meerstern/PS2USB_CONVERTER/firm_v2/src/config/default/initialization.c

/*******************************************************************************
  System Initialization File

  File Name:
    initialization.c

  Summary:
    This file contains source code necessary to initialize the system.

  Description:
    This file contains source code necessary to initialize the system.  It
    implements the "SYS_Initialize" function, defines the configuration bits,
    and allocates any necessary global system resources,
 *******************************************************************************/

// DOM-IGNORE-BEGIN
/*******************************************************************************
* Copyright (C) 2018 Microchip Technology Inc. and its subsidiaries.
*
* Subject to your compliance with these terms, you may use Microchip software
* and any derivatives exclusively with Microchip products. It is your
* responsibility to comply with third party license terms applicable to your
* use of third party software (including open source software) that may
* accompany Microchip software.
*
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
* IN NO EVENT WILL MICROCHIP BE LIABLE FOR ANY INDIRECT, SPECIAL, PUNITIVE,
* INCIDENTAL OR CONSEQUENTIAL LOSS, DAMAGE, COST OR EXPENSE OF ANY KIND
* WHATSOEVER RELATED TO THE SOFTWARE, HOWEVER CAUSED, EVEN IF MICROCHIP HAS
* BEEN ADVISED OF THE POSSIBILITY OR THE DAMAGES ARE FORESEEABLE. TO THE
* FULLEST EXTENT ALLOWED BY LAW, MICROCHIP'S TOTAL LIABILITY ON ALL CLAIMS IN
* ANY WAY RELATED TO THIS SOFTWARE WILL NOT EXCEED THE AMOUNT OF FEES, IF ANY,
* THAT YOU HAVE PAID DIRECTLY TO MICROCHIP FOR THIS SOFTWARE.
 *******************************************************************************/
// DOM-IGNORE-END

// *****************************************************************************
// *****************************************************************************
// Section: Included Files
// *****************************************************************************
// *****************************************************************************
#include "configuration.h"
#include "definitions.h"
#include "device.h"



// ****************************************************************************
// ****************************************************************************
// Section: Configuration Bits
// ****************************************************************************
// ****************************************************************************

/*** DEVCFG0 ***/
#pragma config DEBUG =      OFF
#pragma config JTAGEN =     OFF
#pragma config ICESEL =     ICS_PGx1
#pragma config PWP =        OFF
#pragma config BWP =        OFF
#pragma config CP =         OFF


/*** DEVCFG1 ***/
#pragma config FNOSC =      FRCPLL
#pragma config FPBDIV =     DIV_1
#pragma config FSOSCEN =    OFF
#pragma config IESO =       OFF
#pragma config POSCMOD =    HS
#pragma config OSCIOFNC =   OFF
#pragma config FCKSM =      CSDCMD
#pragma config WDTPS =      PS1048576
#pragma config FWDTEN =     OFF
#pragma config WINDIS =     OFF
#pragma config FWDTWINSZ =  WINSZ_50


/*** DEVCFG2 ***/
#pragma config FPLLIDIV =   DIV_2
#pragma config FPLLMUL =    MUL_20
#pragma config FPLLODIV =   DIV_2
#pragma config UPLLEN =     ON
#pragma config UPLLIDIV =   DIV_3

/*** DEVCFG3 ***/
#pragma config FVBUSONIO =  ON
#pragma config USERID =     0xffff
#pragma config PMDL1WAY =   ON
#pragma config IOL1WAY =    ON
#pragma config FUSBIDIO =   OFF




// *****************************************************************************
// *****************************************************************************
// Section: Driver Initialization Data
// *****************************************************************************
// *****************************************************************************


// *****************************************************************************
// *****************************************************************************
// Section: System Data
// *****************************************************************************
// *****************************************************************************
/* Structure to hold the object handles for the modules in the system. */
SYSTEM_OBJECTS sysObj;

// *****************************************************************************
// *****************************************************************************
// Section: Library/Stack Initialization Data
// *****************************************************************************
// *****************************************************************************
/******************************************************
 * USB Driver Initialization
 ******************************************************/
 
uint8_t __attribute__((aligned(512))) endPointTable1[DRV_USBFS_ENDPOINTS_NUMBER * 32];

void DRV_USB_VBUSPowerEnable(uint8_t port, bool enable)
{
	/* Note: USB Host applications should have a way for Enabling/Disabling the 
	   VBUS. Applications can use a GPIO to turn VBUS on/off through a switch. 
	   In MHC Pin Settings select the pin used as VBUS Power Enable as output and 
	   name it to "VBUS_AH". If you a see a build error from this function either 
	   you have not configured the VBUS Power Enable in MHC pin settings or the 
	   Pin name entered in MHC is not "VBUS_AH". */ 
    if (enable == true)
	{
		/* Enable the VBUS */
		//VBUS_AH_PowerEnable();
	}
	else
	{
		/* Disable the VBUS */
		//VBUS_AH_PowerDisable();
	}
}

const DRV_USBFS_INIT drvUSBFSInit =
{
	 /* Assign the endpoint table */
    .endpointTable= endPointTable1,


	/* Interrupt Source for USB module */
	.interruptSource = INT_SOURCE_USB,

    
	/* USB Controller to operate as USB Host */
    .operationMode = DRV_USBFS_OPMODE_HOST,
	
	.operationSpeed = USB_SPEED_FULL,
 
	/* Stop in idle */
    .stopInIdle = false,
	
	    /* Suspend in sleep */
    .suspendInSleep = false,
 
    /* Identifies peripheral (PLIB-level) ID */
    .usbID = USB_ID_1,
	
	/* USB Host Power Enable. USB Driver uses this function to Enable the VBUS */ 
	.portPowerEnable = DRV_USB_VBUSPowerEnable,
	
    /* Root hub available current in milliamperes */
    .rootHubAvailableCurrent = 500,

};








// *****************************************************************************
// *****************************************************************************
// Section: System Initialization
// *****************************************************************************
// *****************************************************************************
// <editor-fold defaultstate="collapsed" desc="SYS_CONSOLE Instance 0 Initialization Data">


/* Declared in console device implementation (sys_console_uart.c) */
extern const SYS_CONSOLE_DEV_DESC sysConsoleUARTDevDesc;

const SYS_CONSOLE_UART_PLIB_INTERFACE sysConsole0UARTPlibAPI =
{
    .read = (SYS_CONSOLE_UART_PLIB_READ)UART2_Read,
	.readCountGet = (SYS_CONSOLE_UART_PLIB_READ_COUNT_GET)UART2_ReadCountGet,
	.readFreeBufferCountGet = (SYS_CONSOLE_UART_PLIB_READ_FREE_BUFFFER_COUNT_GET)UART2_ReadFreeBufferCountGet,
    .write = (SYS_CONSOLE_UART_PLIB_WRITE)UART2_Write,
	.writeCountGet = (SYS_CONSOLE_UART_PLIB_WRITE_COUNT_GET)UART2_WriteCountGet,
	.writeFreeBufferCountGet = (SYS_CONSOLE_UART_PLIB_WRITE_FREE_BUFFER_COUNT_GET)UART2_WriteFreeBufferCountGet,
};

const SYS_CONSOLE_UART_INIT_DATA sysConsole0UARTInitData =
{
    .uartPLIB = &sysConsole0UARTPlibAPI,    
};

const SYS_CONSOLE_INIT sysConsole0Init =
{
    .deviceInitData = (const void*)&sysConsole0UARTInitData,
    .consDevDesc = &sysConsoleUARTDevDesc,
    .deviceIndex = 0,
};



// </editor-fold>


const SYS_DEBUG_INIT debugInit =
{
    .moduleInit = {0},
    .errorLevel = SYS_DEBUG_GLOBAL_ERROR_LEVEL,
    .consoleIndex = 0,
};


// <editor-fold defaultstate="collapsed" desc="SYS_TIME Initialization Data">

const SYS_TIME_PLIB_INTERFACE sysTimePlibAPI = {
    .timerCallbackSet = (SYS_TIME_PLIB_CALLBACK_REGISTER)CORETIMER_CallbackSet,
    .timerStart = (SYS_TIME_PLIB_START)CORETIMER_Start,
    .timerStop = (SYS_TIME_PLIB_STOP)CORETIMER_Stop ,
    .timerFrequencyGet = (SYS_TIME_PLIB_FREQUENCY_GET)CORETIMER_FrequencyGet,
    .timerPeriodSet = (SYS_TIME_PLIB_PERIOD_SET)NULL,
    .timerCompareSet = (SYS_TIME_PLIB_COMPARE_SET)CORETIMER_CompareSet,
    .timerCounterGet = (SYS_TIME_PLIB_COUNTER_GET)CORETIMER_CounterGet,
};

const SYS_TIME_INIT sysTimeInitData =
{
    .timePlib = &sysTimePlibAPI,
    .hwTimerIntNum = 0,
};

// </editor-fold>



// *****************************************************************************
// *****************************************************************************
// Section: Local initialization functions
// *****************************************************************************
// *****************************************************************************



/*******************************************************************************
  Function:
    void SYS_Initialize ( void *data )

  Summary:
    Initializes the board, services, drivers, application and other modules.

  Remarks:
 */

void SYS_Initialize ( void* data )
{

    /* Start out with interrupts disabled before configuring any modules */
    __builtin_disable_interrupts();

  
    CLK_Initialize();

    /* Configure KSEG0 as cacheable memory. This is needed for Prefetch Buffer */
    __builtin_mtc0(16, 0,(__builtin_mfc0(16, 0) | 0x3));

    /* Set the SRAM wait states to zero */
    BMXCONbits.BMXWSDRM = 0;




	GPIO_Initialize();

    CORETIMER_Initialize();
	UART2_Initialize();



    sysObj.sysConsole0 = SYS_CONSOLE_Initialize(SYS_CONSOLE_INDEX_0, (SYS_MODULE_INIT *)&sysConsole0Init);

    sysObj.sysDebug = SYS_DEBUG_Initialize(SYS_DEBUG_INDEX_0, (SYS_MODULE_INIT*)&debugInit);


    sysObj.sysTime = SYS_TIME_Initialize(SYS_TIME_INDEX_0, (SYS_MODULE_INIT *)&sysTimeInitData);

	/* Initialize the USB Host layer */
    sysObj.usbHostObject0 = USB_HOST_Initialize (( SYS_MODULE_INIT *)& usbHostInitData );	

	/* Initialize USB Driver */ 
    sysObj.drvUSBFSObject = DRV_USBFS_Initialize(DRV_USBFS_INDEX_0, (SYS_MODULE_INIT *) &drvUSBFSInit);	


    APP_Initialize();


    EVIC_Initialize();

	/* Enable global interrupts */
    __builtin_enable_interrupts();


}


/*******************************************************************************
 End of File
*/
